Emile666/C100_pid_stm8s105/src/pid.c

/*==================================================================
  File name    : pid.c
  Author       : Emile
  ------------------------------------------------------------------
  Purpose : This file contains the main body of the PID controller.

           For design details, please check:
           document: PID_Controller_Calculus.pdf
           website : http://www.vandelogt.nl/uk_regelen_pid.php

            With the GUI, the following parameters can be changed:
            Kc: The controller gain in %/Â°C
            Ti: Time-constant for the Integral Gain in seconds
            Td: Time-constant for the Derivative Gain in seconds
            Ts: The sample period in seconds
  ------------------------------------------------------------------
  STC1000+ is free software: you can redistribute it and/or modify
  it under the terms of the GNU General Public License as published by
  the Free Software Foundation, either version 3 of the License, or
  (at your option) any later version.
 
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
  You should have received a copy of the GNU General Public License
  along with STC1000+.  If not, see <http://www.gnu.org/licenses/>.
  ------------------------------------------------------------------
  $Log: $
  ==================================================================
*/
#include "pid.h"

uint16_t kc = 0;   // Parameter value for Kc value in %/Â°C
uint16_t ti = 0;   // Parameter value for I action in seconds
uint16_t td = 0;   // Parameter value for D action in seconds
// Init ts to 0 to disable pid-control and enable thermostat control
uint8_t  ts = 0;   // Parameter value for sample time [sec.]
uint32_t ki;       // Internal value for I action
uint32_t kd;       // Internal value for D action
int32_t  pp;       // debug
int16_t  yk_1;     // y[k-1]
int16_t  yk_2;     // y[k-2]
int16_t  pid_max;
int16_t  pid_min;

/*------------------------------------------------------------------
  Purpose  : This function initialises the Takahashi Type C PID
             controller.
  Variables: kc: Kc parameter value in %/°C    ; controls P-action
             ti: Ti parameter value in seconds ; controls I-action
             td: Td parameter value in seconds ; controls D-action
             ts: Ts parameter sample-time of pid-controller in seconds
             yk: actual temperature value

                   Kc.Ts
             ki =  -----   (for I-term)
                    Ti

                       Td
             kd = Kc . --  (for D-term)
                       Ts

  Returns  : No values are returned
  ------------------------------------------------------------------*/
void init_pid(uint16_t kc, uint16_t ti, uint16_t td, uint8_t ts, int16_t yk)
{
   if (ti == 0) ki = 0;
   else         ki = (((uint32_t)kc * ts) / ti);
   if (ts == 0) kd = 0;
   else         kd = (((uint32_t)kc * td) / ts);

   if (kc > 0)
   {   // heating loop
       pid_max = GMA_HLIM;
       pid_min = 0;
   }
   else
   {   // cooling loop
       pid_max = 0;
       pid_min = GMA_LLIM;
   } // else
   yk_2 = yk_1 = yk; // init. previous samples to current temperature
} // init_pid()

/*------------------------------------------------------------------
  Purpose  : This function implements the Takahashi Type C PID
             controller: the P and D term are no longer dependent
             on the setpoint, only on PV.
             This function should be called once every TS seconds.
  Variables:
        yk : The input variable y[k] (= measured temperature in E-1 °C)
       *uk : The pid-output variable u[k] [-1000..+1000] in E-1 %
      tset : The setpoint value w[k] for the temperature in E-1 °C
  Returns  : No values are returned
  ------------------------------------------------------------------*/
void pid_ctrl(int16_t yk, int16_t *uk, int16_t tset)
{
    //-----------------------------------------------------------------------------
    // Takahashi Type C PID controller:
    //
    // e[k] = w[k] - y[k]
    //                                    Kc.Ts        Kc.Td
    // u[k] = u[k-1] + Kc.(y[k-1]-y[k]) + -----.e[k] + -----.(2.y[k-1]-y[k]-y[k-2])
    //                                      Ti           Ts
    //
    //-----------------------------------------------------------------------------
    pp   = (uint32_t)kc * (yk_1 - yk);               // Kc.(y[k-1]-y[k])
    pp  += (uint32_t)ki * (tset - yk);               // (Kc.Ts/Ti).e[k]
    pp  += (uint32_t)kd * ((yk_1 << 1) - yk - yk_2); // (Kc.Td/Ts).(2.y[k-1]-y[k]-y[k-2])
    *uk += (int16_t)pp;
    // limit u[k] to maximum and minimum values
    if (*uk > pid_max)      *uk = pid_max;
    else if (*uk < pid_min) *uk = pid_min;

    yk_2  = yk_1; // y[k-2] = y[k-1]
    yk_1  = yk;   // y[k-1] = y[k]
} // pid_ctrl()

void pid_auto_tuning(void)
{
} // pid_auto_tuning()
